ithinuel/wilskeeb/media/wilskeeb_2.png

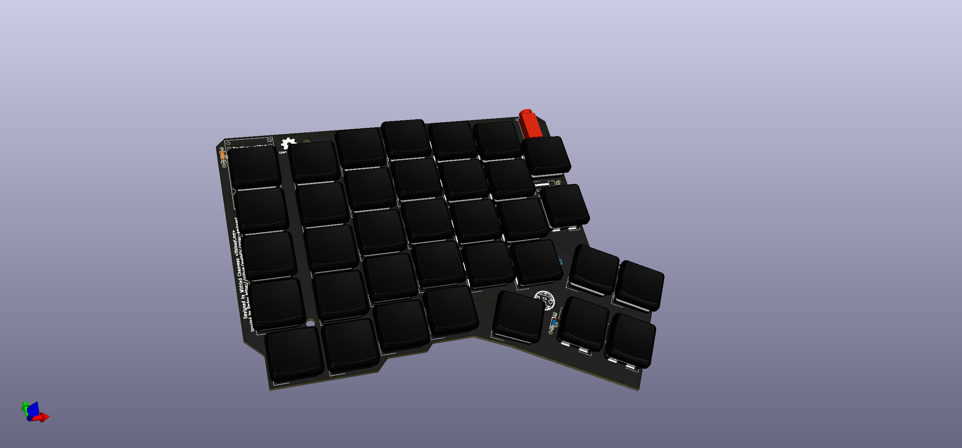
media/wilskeeb_2.png
