ithinuel/wilskeeb/media/wilskeeb_4.png

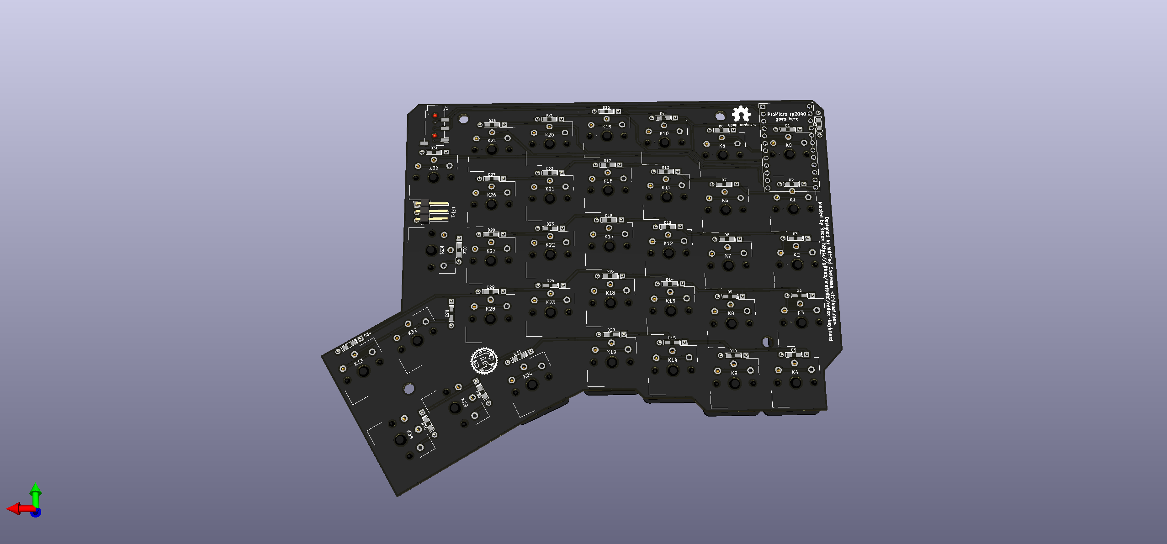
media/wilskeeb_4.png
