ithinuel/wilskeeb/media/wilskeeb_5.png

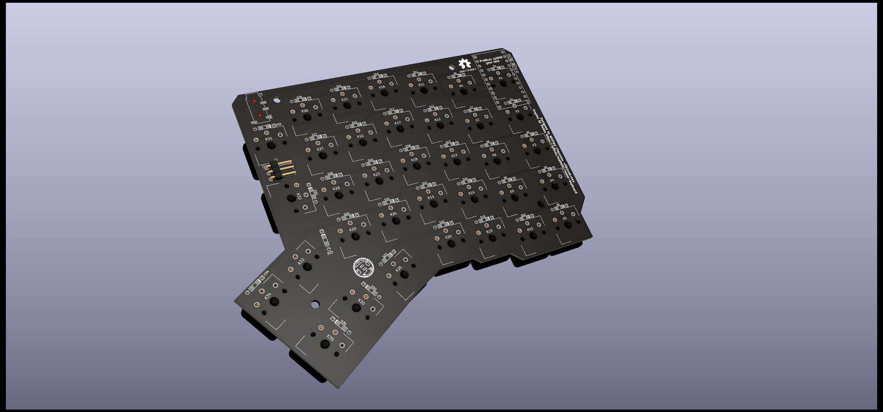
media/wilskeeb_5.png
