ithinuel/wilskeeb/media/wilskeeb_left_back.png

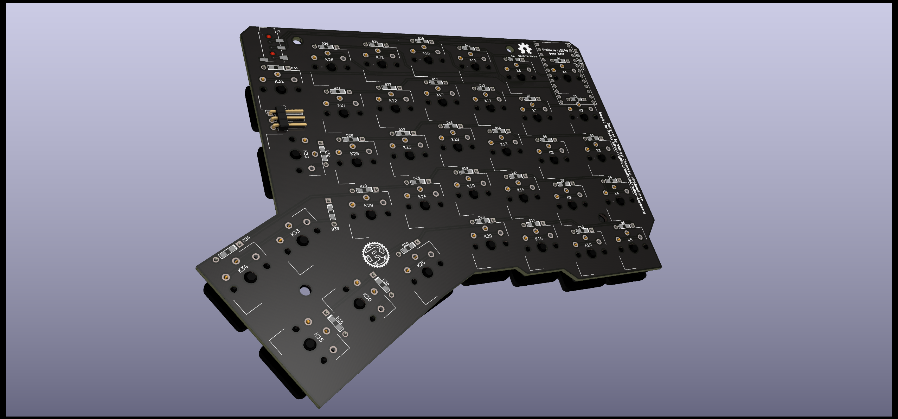
media/wilskeeb_left_back.png
